newaetech/chipshouter-picoemp/hardware/SCH-PICOEMP-REV04_Page_1.png

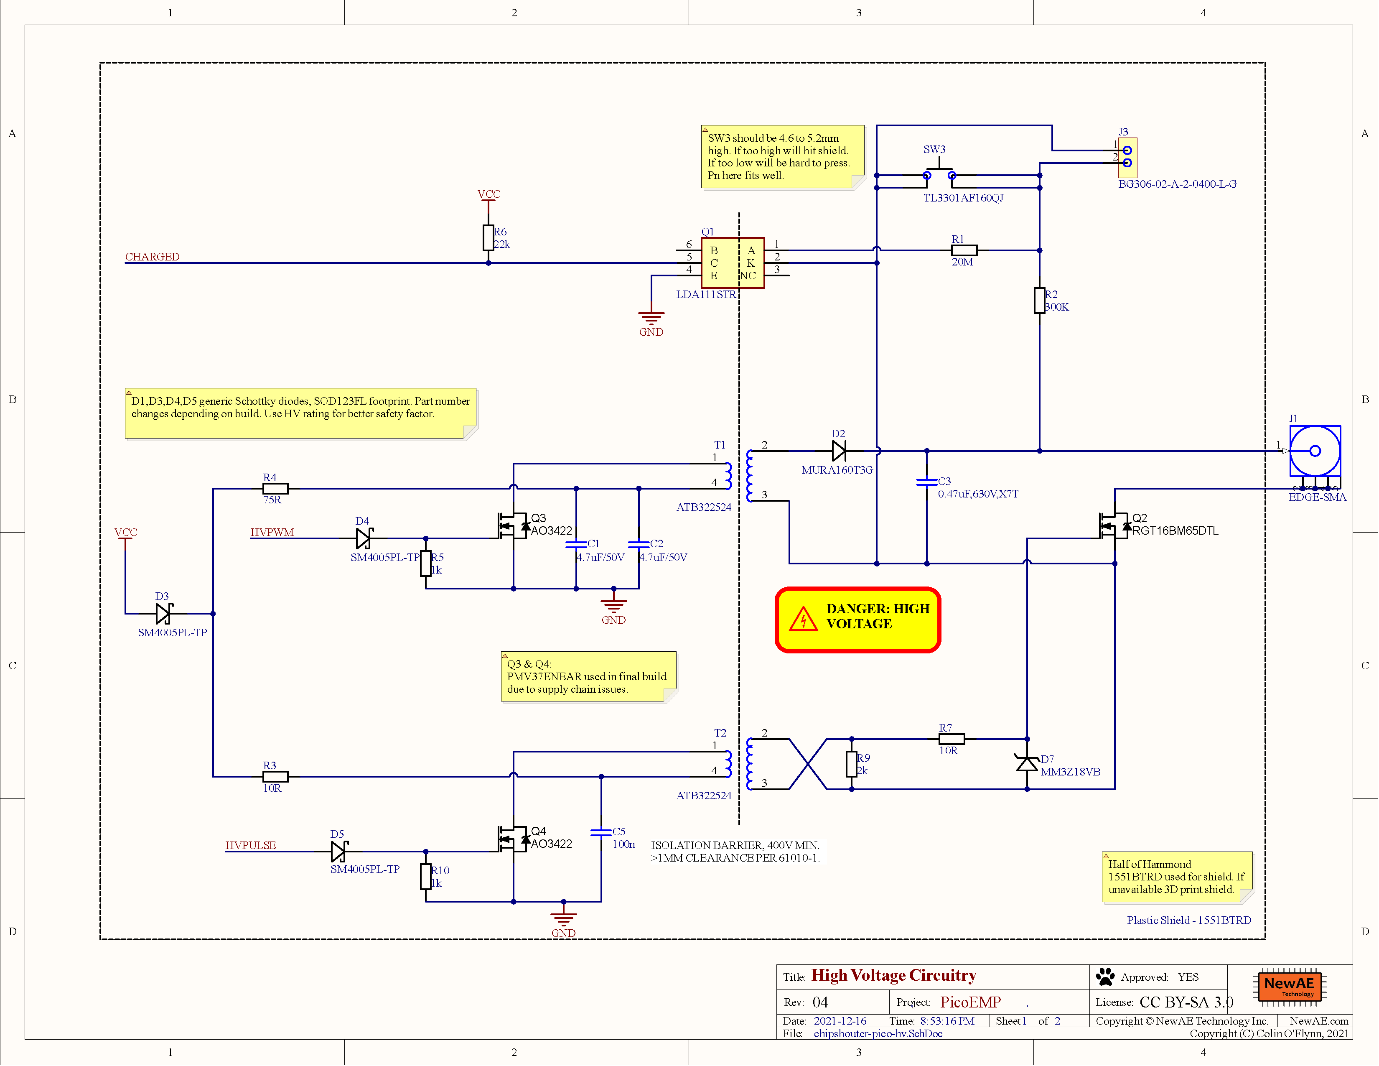
hardware/SCH-PICOEMP-REV04_Page_1.png
