newaetech/chipshouter-picoemp/hardware/SCH-PICOEMP-REV04_Page_2.png

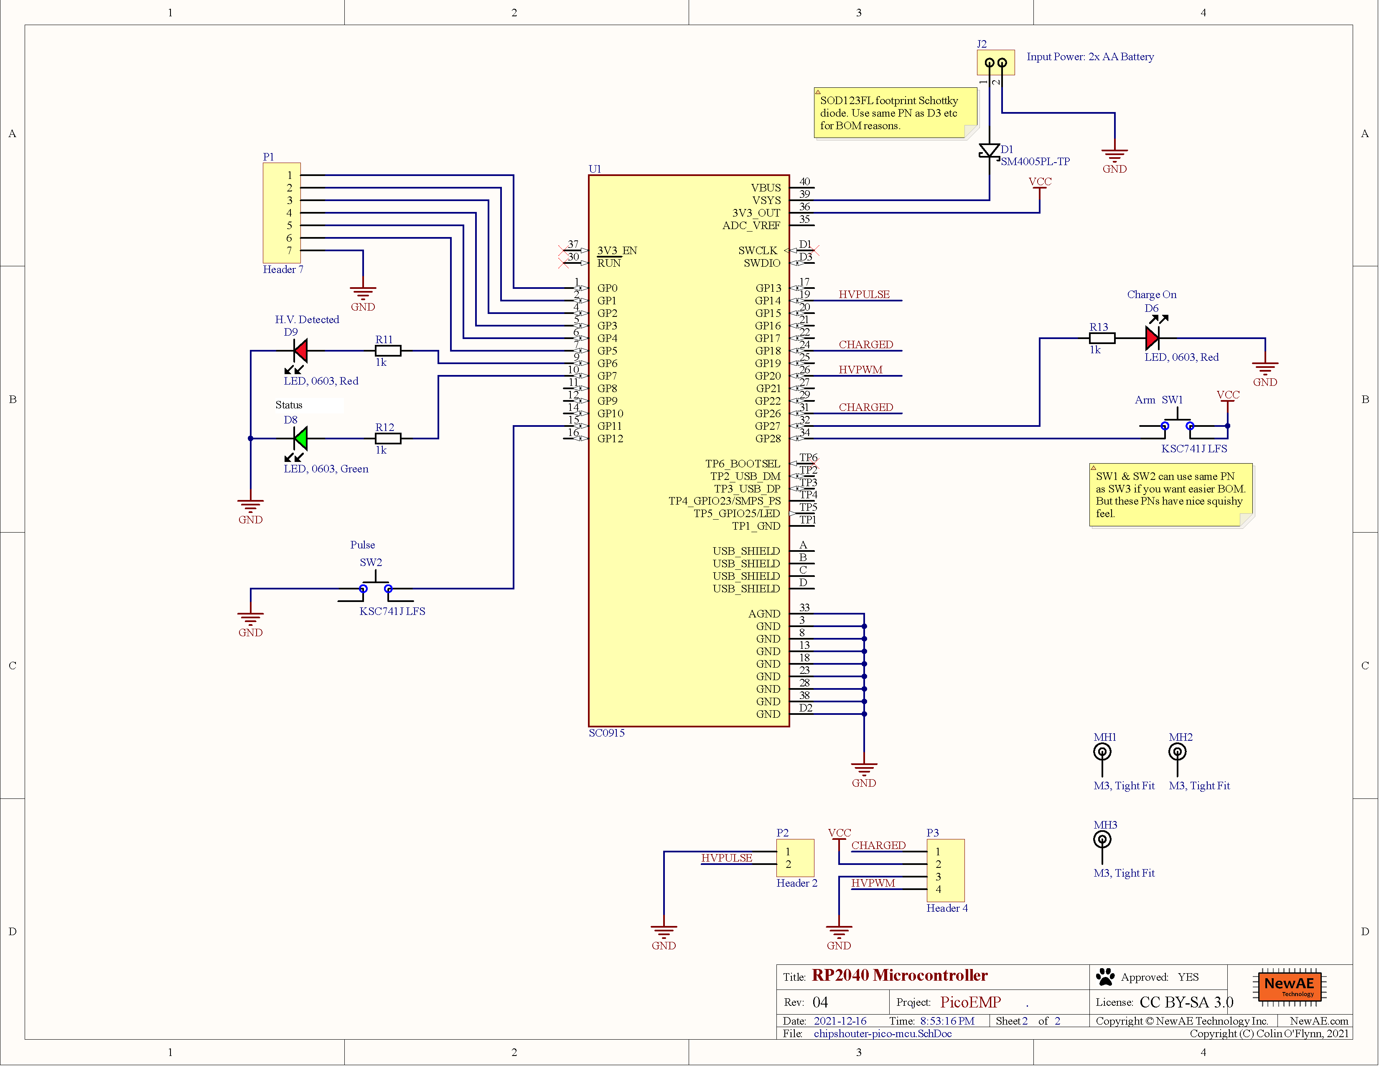
hardware/SCH-PICOEMP-REV04_Page_2.png
